lung-sta/EEE4022S_2025_MBSLUN011/Point_Clouds/e1_g_hres.png

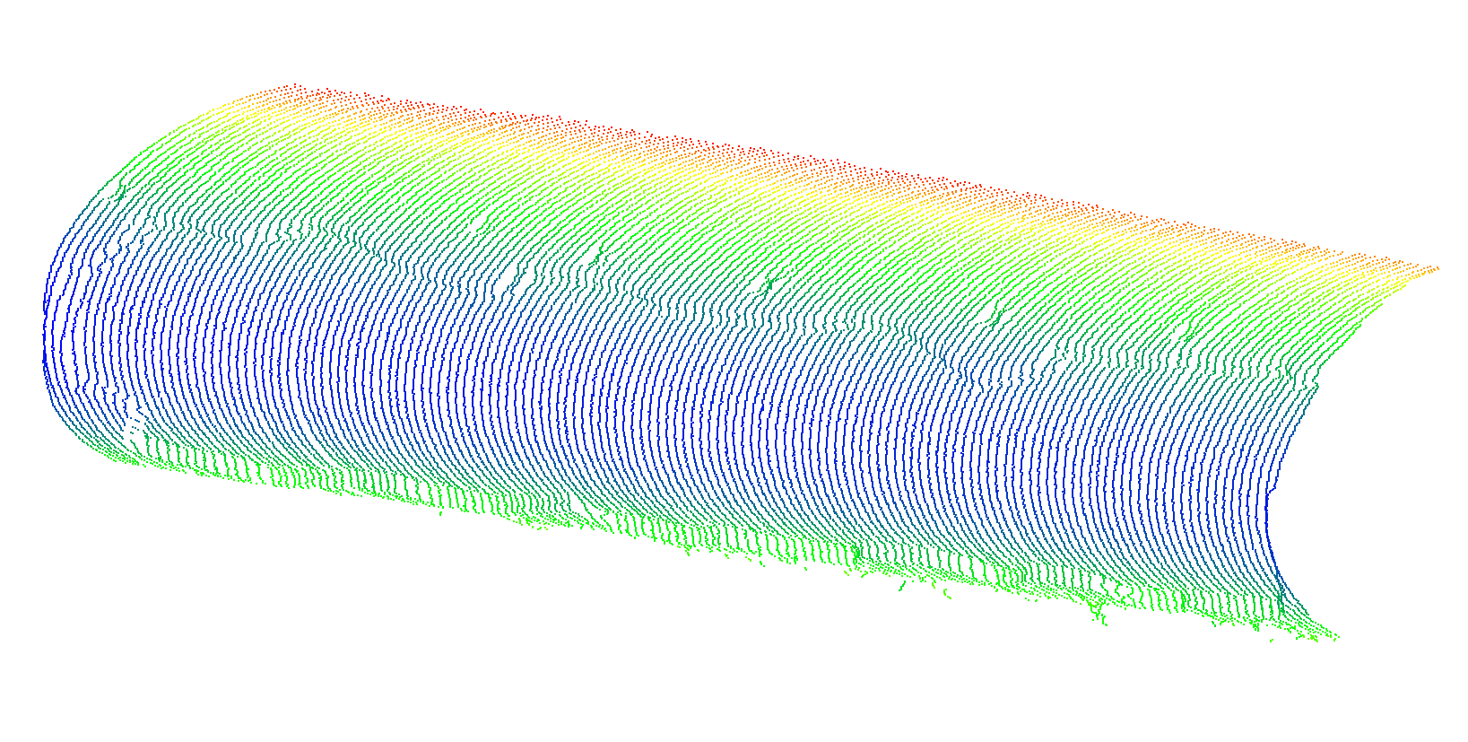
Point_Clouds/e1_g_hres.png
