lung-sta/EEE4022S_2025_MBSLUN011/Point_Clouds/hist_blank_ghres.png

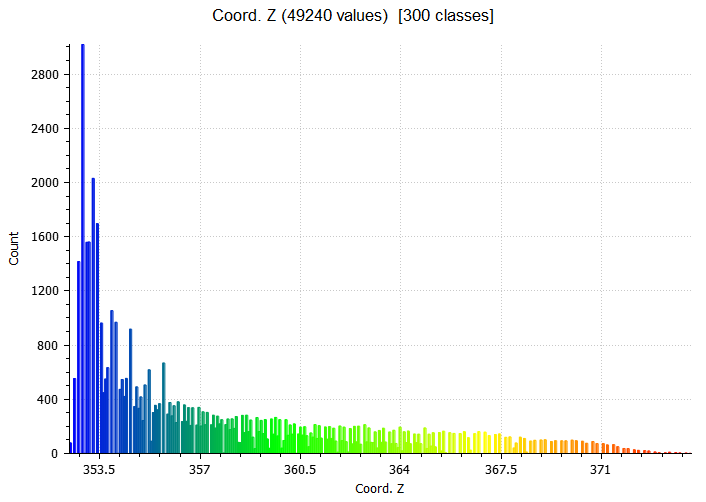
Point_Clouds/hist_blank_ghres.png
