lung-sta/EEE4022S_2025_MBSLUN011/Point_Clouds/hist_e1_rlres.png

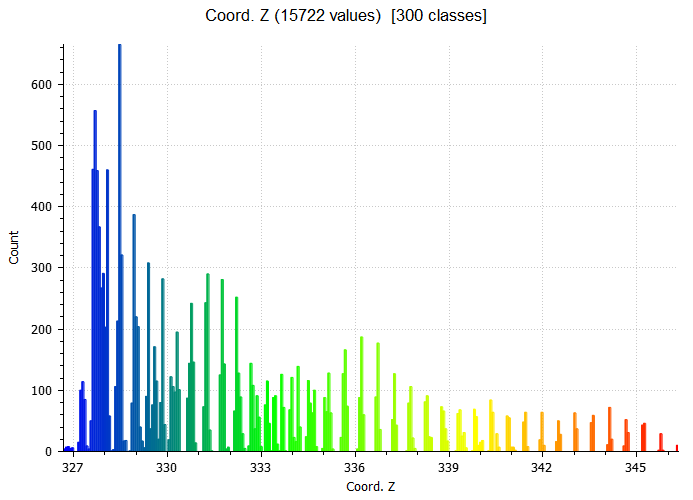
Point_Clouds/hist_e1_rlres.png
