lung-sta/EEE4022S_2025_MBSLUN011/Point_Clouds/v1_r_lres.png

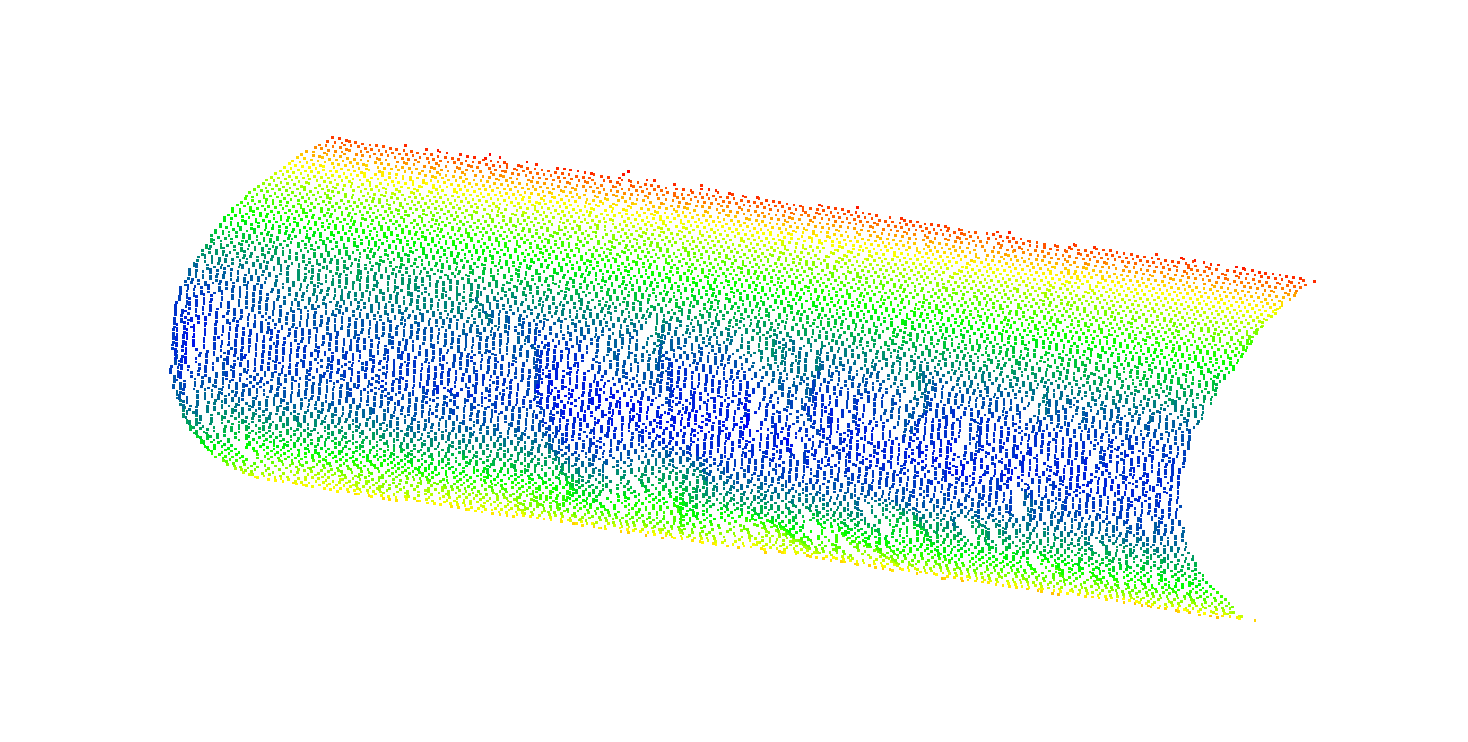
Point_Clouds/v1_r_lres.png
